nocoolnicksleft/NumitronClock/Images/500_numitron-10.JPG

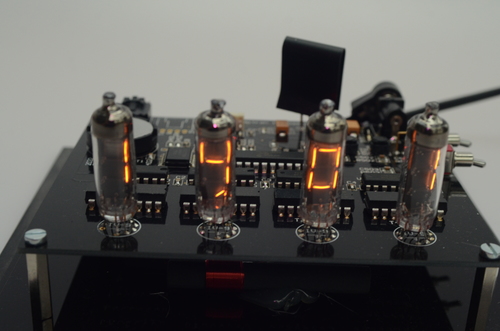
Images/500_numitron-10.JPG
