nocoolnicksleft/NumitronClock/Images/500_numitron-12.JPG

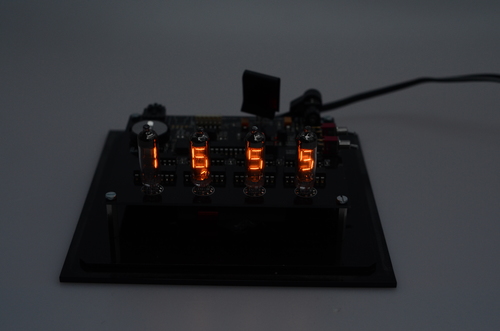
Images/500_numitron-12.JPG
